sdebby/3NCRYP2P_2/media/3ncryp2p last of us.png

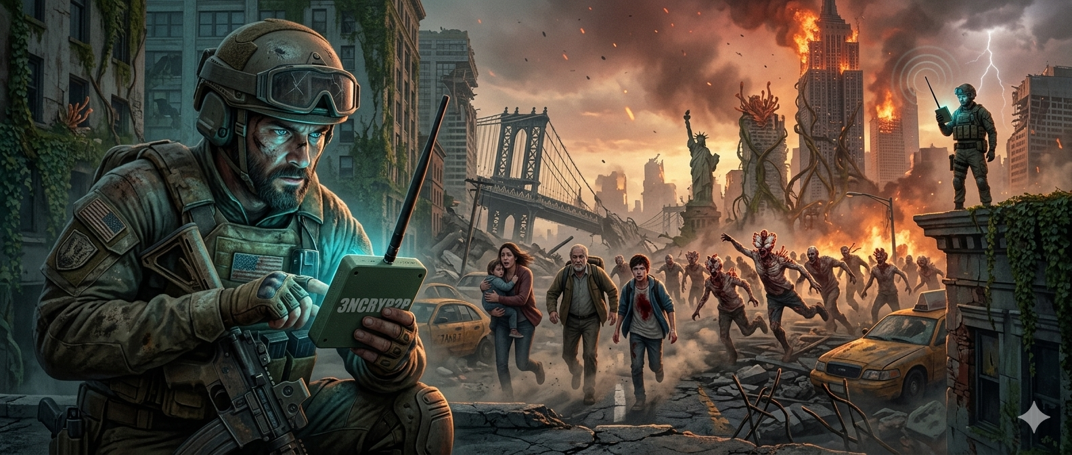
media/3ncryp2p last of us.png
